Grooviee/e-ink-tap-handle/data/beerinfo.bmp

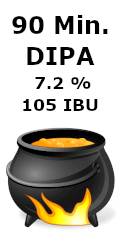
data/beerinfo.bmp
